jusdisgi/stactyl/output/points/units.yaml

U: 19.05
u: 19
cx: 18
cy: 17
$default_stagger: 0
$default_spread: 19
$default_splay: 0
$default_height: 18
$default_width: 18
$default_padding: 19
$default_autobind: 10
kx: 16
ky: 16
ks: 17
kp: 17
kcow: 16
kcoh: 16
keycw: 16
keych: 16
signal_trace_width: 0.2
pwr_trace_width: 0.25
gnd_trace_width: 0.25
via_size: 0.5
via_drill: 0.3
stagger_finger_pinky: -4
stagger_finger_ring: 3
stagger_finger_middle: 5
stagger_finger_index: 0
stagger_finger_inner: -2
splay_finger_pinky: 0
splay_finger_ring: 0
splay_finger_middle: 0
splay_finger_index: 0
splay_finger_inner: 0
